EitanTal/hunter/PCB/IMG_20210823_182307683a.jpg

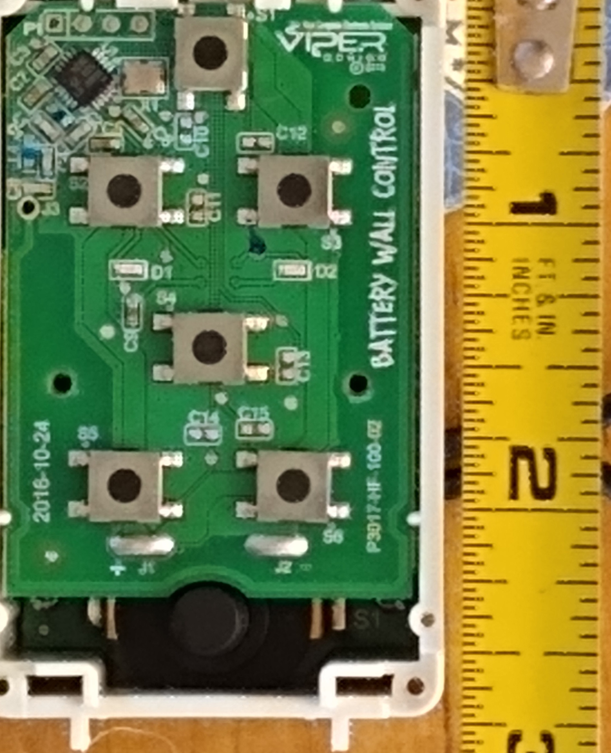
PCB/IMG_20210823_182307683a.jpg
