EitanTal/hunter/circuit/Circuit-ExistingRemote.PNG

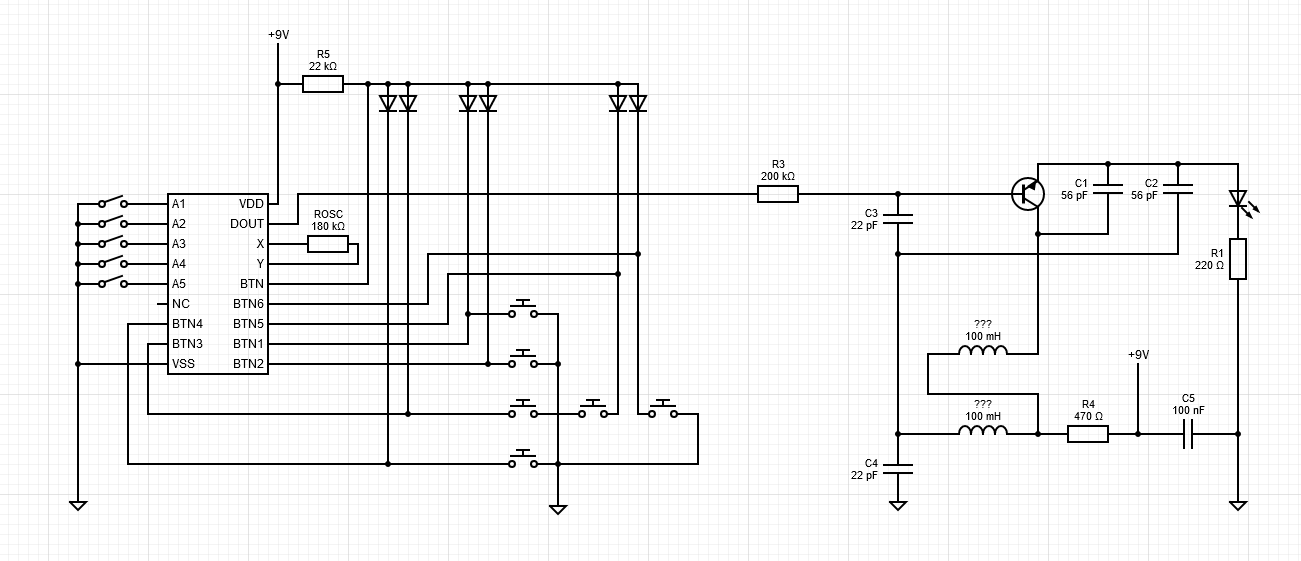
circuit/Circuit-ExistingRemote.PNG
