EitanTal/hunter/PCB/IMG_20210823_162859296.jpg

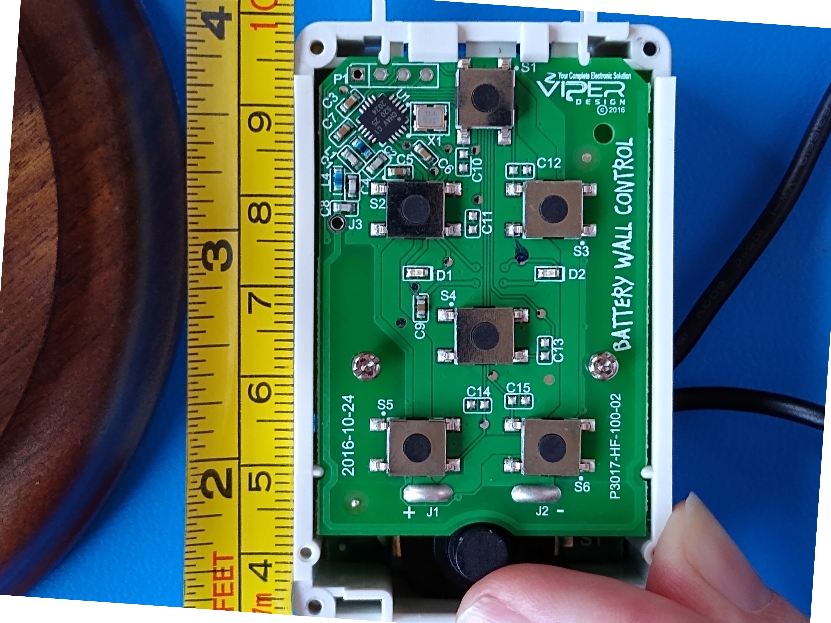
PCB/IMG_20210823_162859296.jpg
