EitanTal/hunter/PCB/other_formfactor.jpg

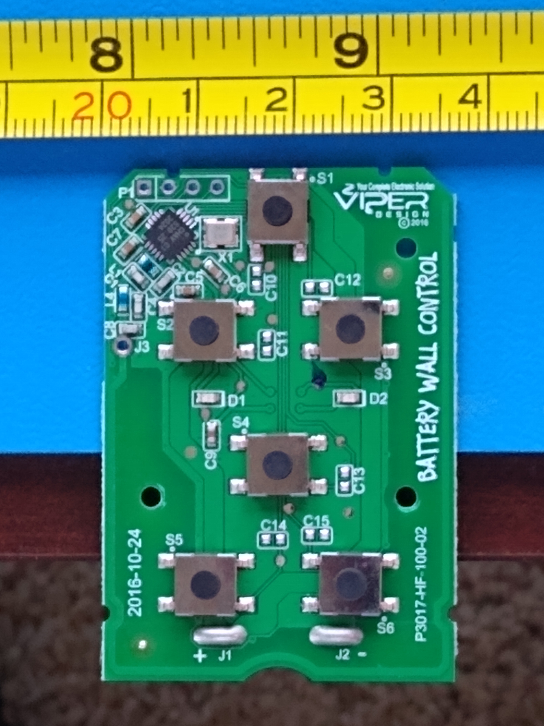
PCB/other_formfactor.jpg
