EitanTal/hunter/SDR/AM-Demodulated.PNG

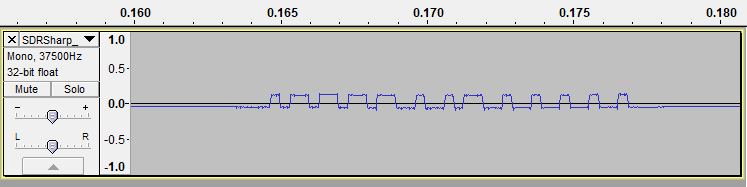
SDR/AM-Demodulated.PNG
