EitanTal/hunter/SDR/SDR_sharp.png

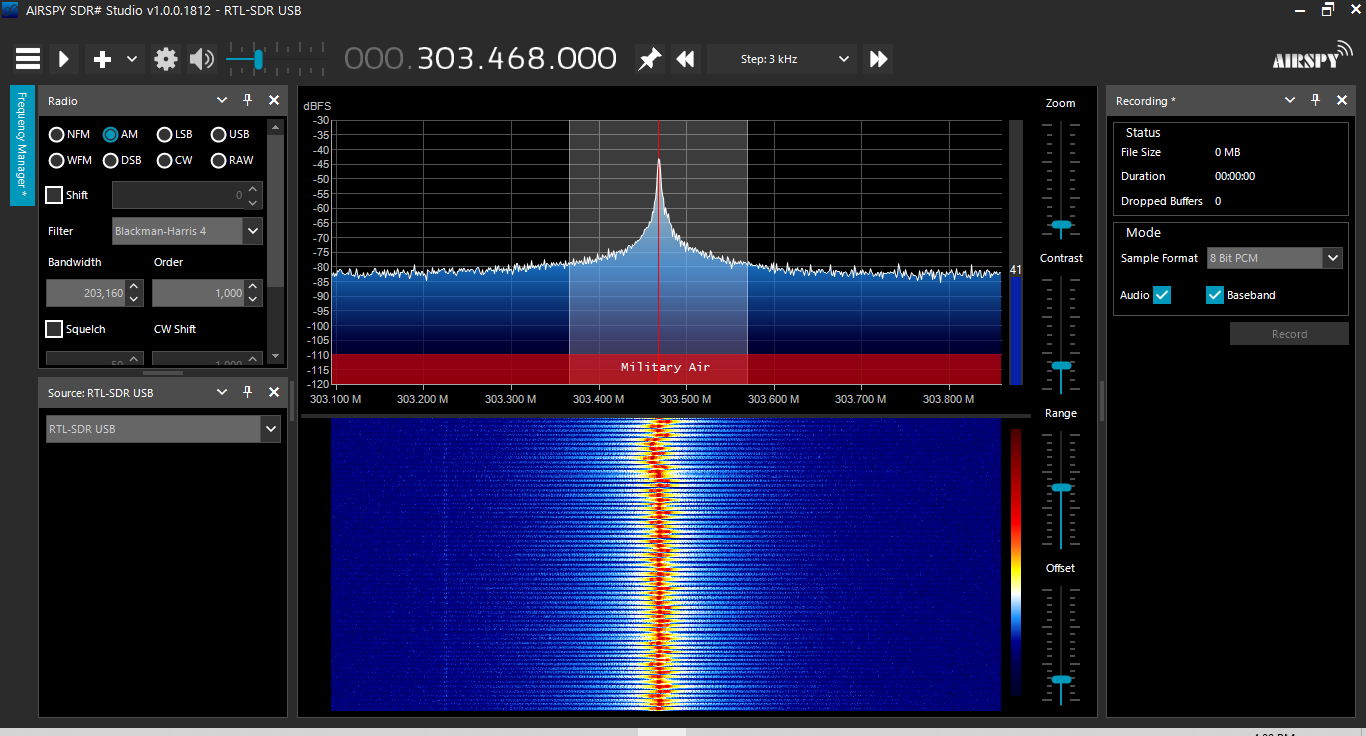
SDR/SDR_sharp.png
