EitanTal/hunter/waveforms/circuit.png

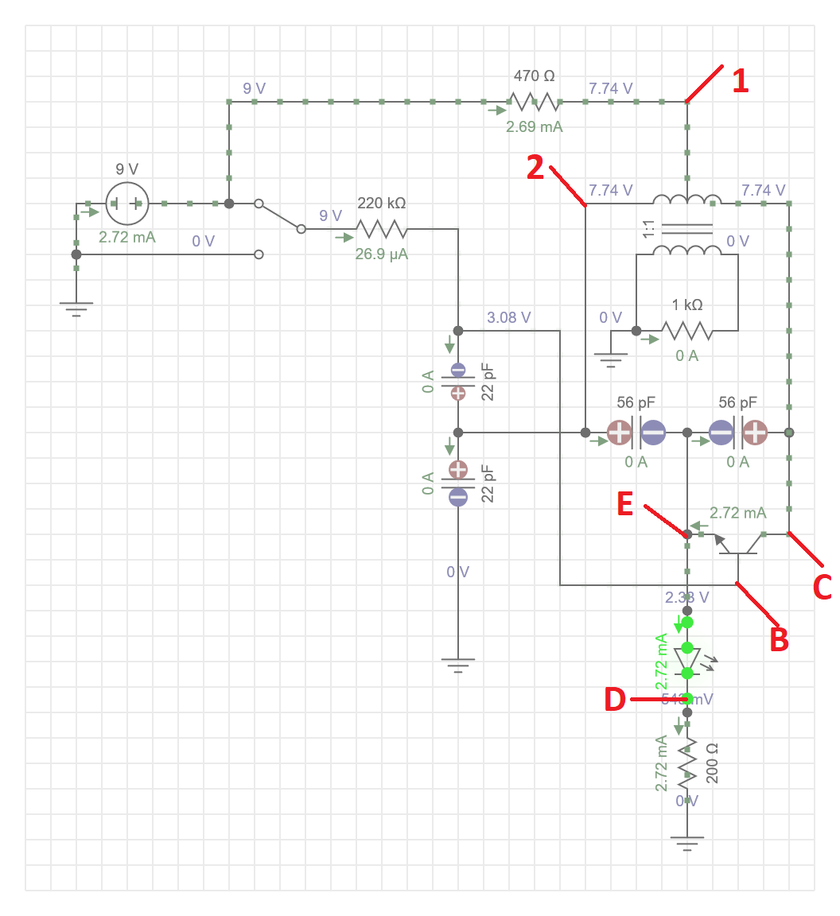
waveforms/circuit.png
