EitanTal/hunter/waveforms/digital_out.png

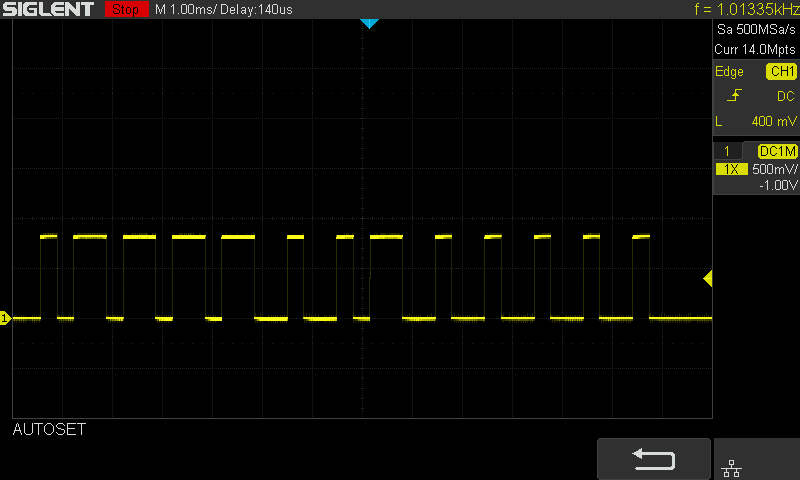
waveforms/digital_out.png
