EitanTal/hunter/waveforms/hunter_base_all.png

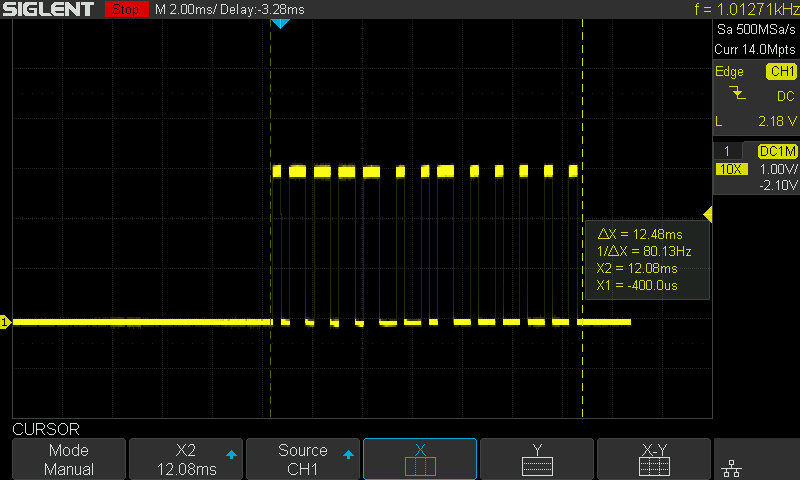
waveforms/hunter_base_all.png
