EitanTal/hunter/waveforms/hunter_base_fall.png

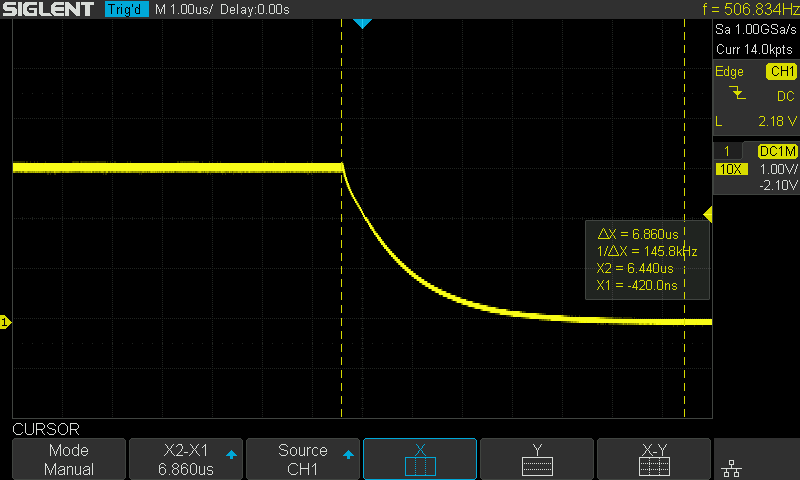
waveforms/hunter_base_fall.png
