EitanTal/hunter/waveforms/hunter_base_h.png

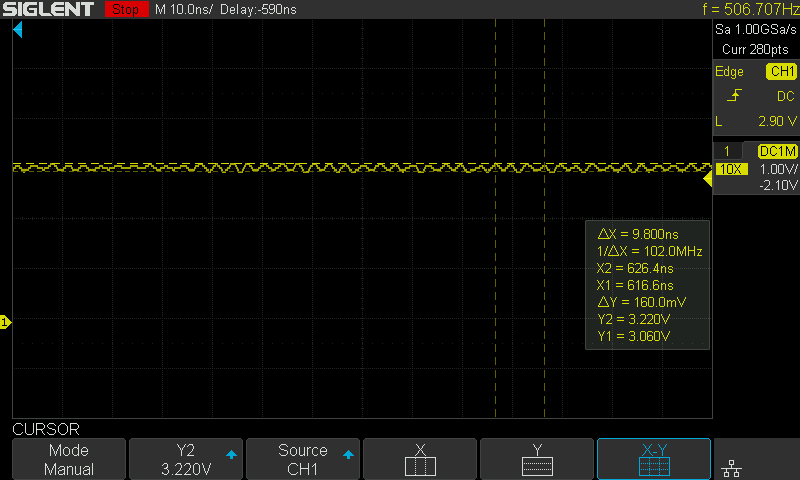
waveforms/hunter_base_h.png
