EitanTal/hunter/waveforms/hunter_base_l.png

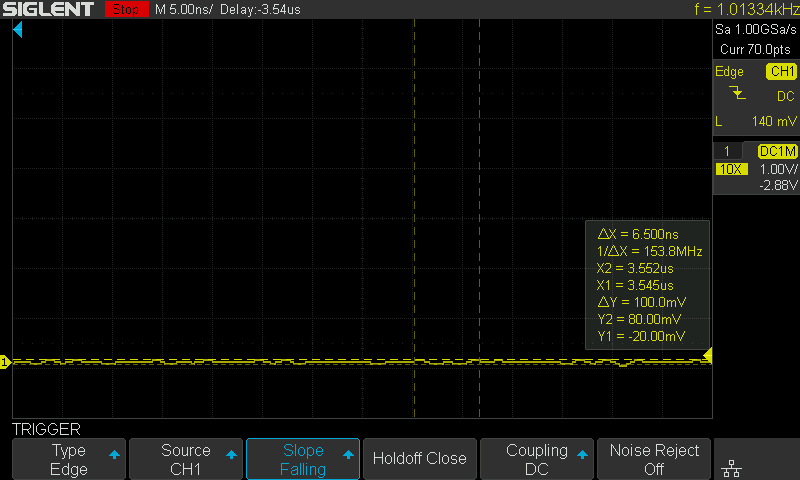
waveforms/hunter_base_l.png
