EitanTal/hunter/waveforms/hunter_collector_all.png

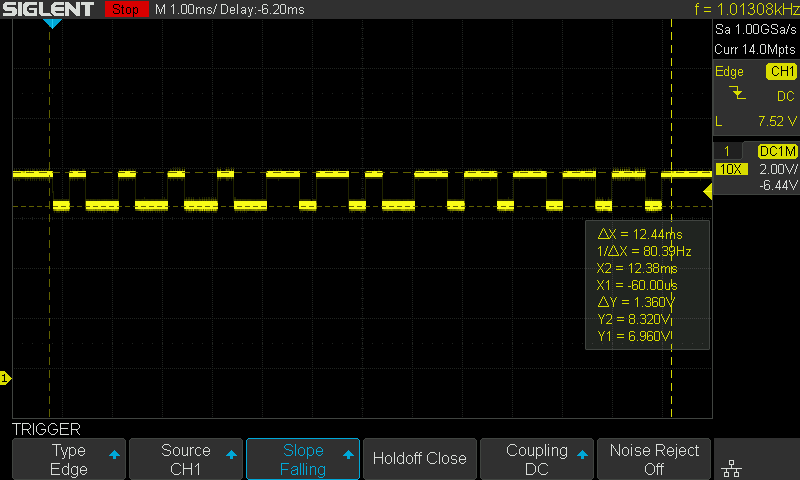
waveforms/hunter_collector_all.png
