EitanTal/hunter/waveforms/hunter_collector_rise.png

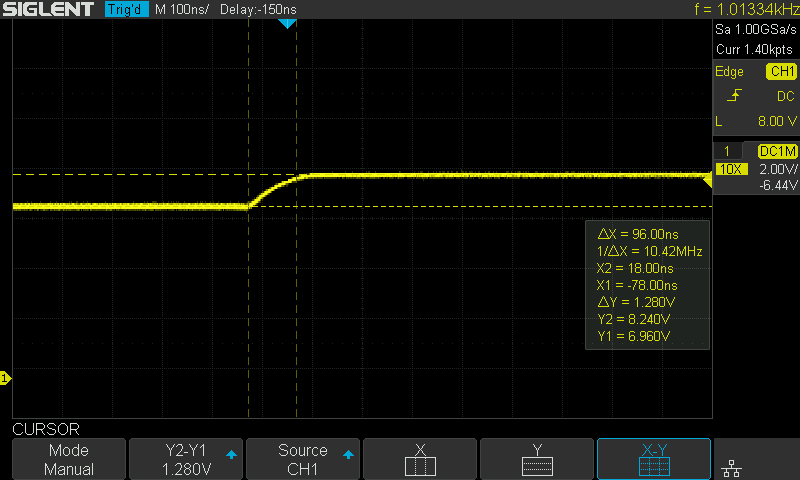
waveforms/hunter_collector_rise.png
