EitanTal/hunter/waveforms/hunter_collector_rise_zoom2.png

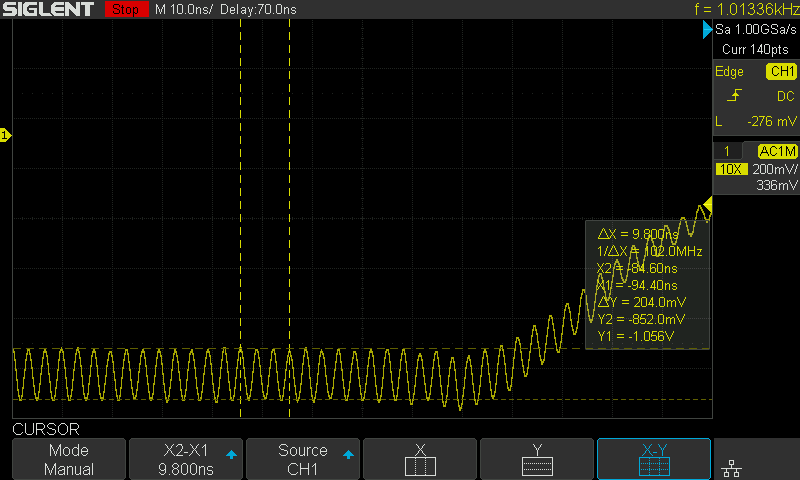
waveforms/hunter_collector_rise_zoom2.png
