EitanTal/hunter/waveforms/hunter_collector_rise_zoom.png

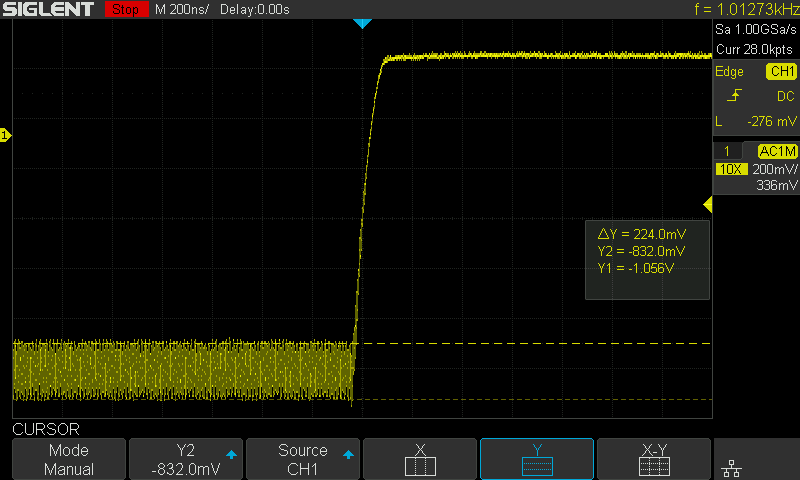
waveforms/hunter_collector_rise_zoom.png
