EitanTal/hunter/waveforms/hunter_diode.png

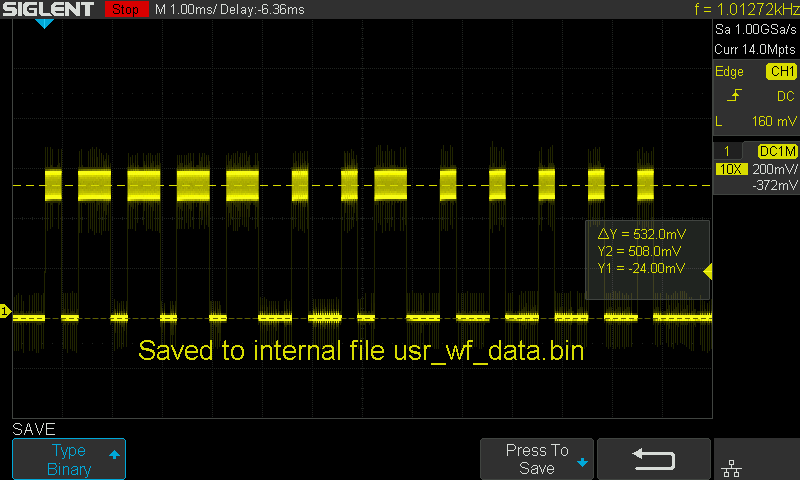
waveforms/hunter_diode.png
