EitanTal/hunter/waveforms/hunter_diode_l.png

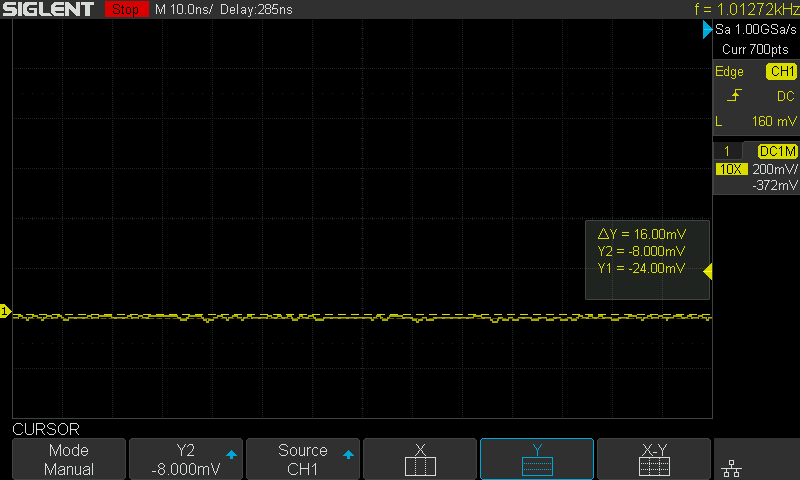
waveforms/hunter_diode_l.png
