EitanTal/hunter/waveforms/hunter_diode_transition.png

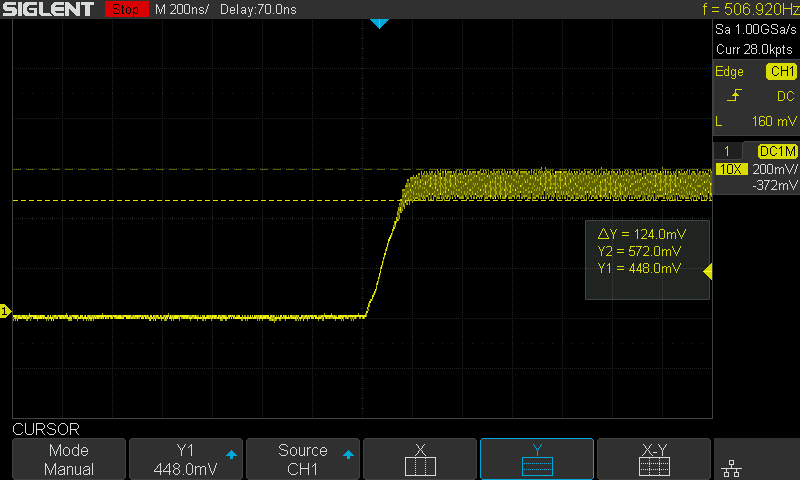
waveforms/hunter_diode_transition.png
