EitanTal/hunter/waveforms/hunter_emitter.png

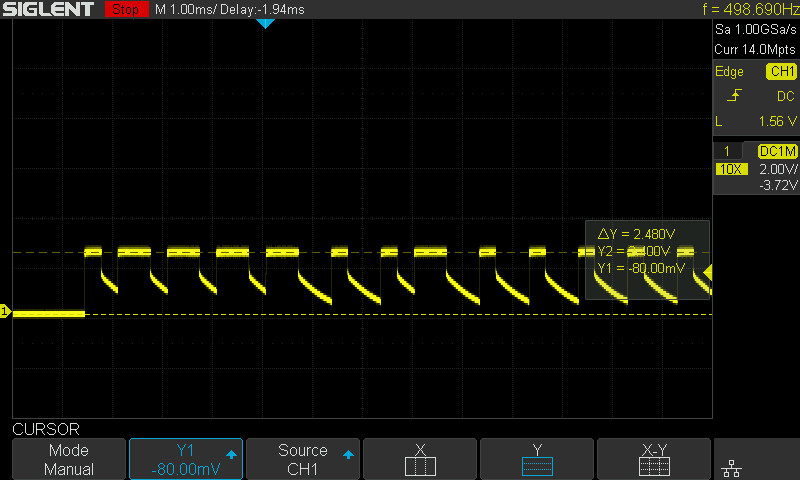
waveforms/hunter_emitter.png
