EitanTal/hunter/waveforms/hunter_emitter_fall.png

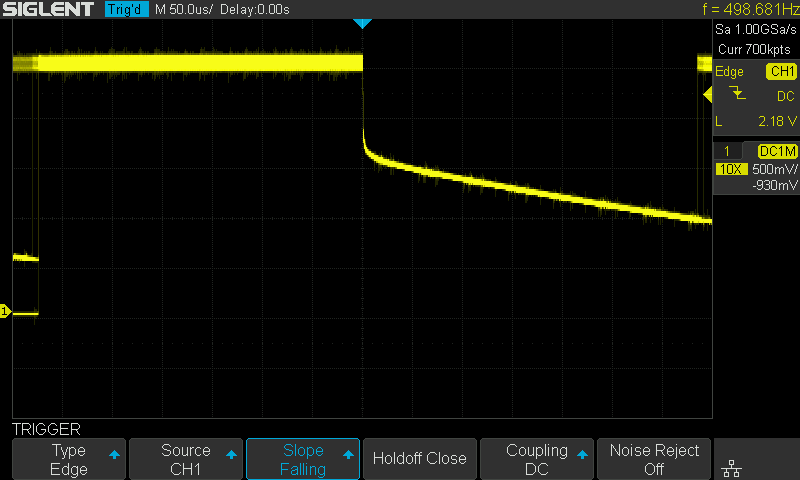
waveforms/hunter_emitter_fall.png
