EitanTal/hunter/waveforms/hunter_emitter_fall_zoom.png

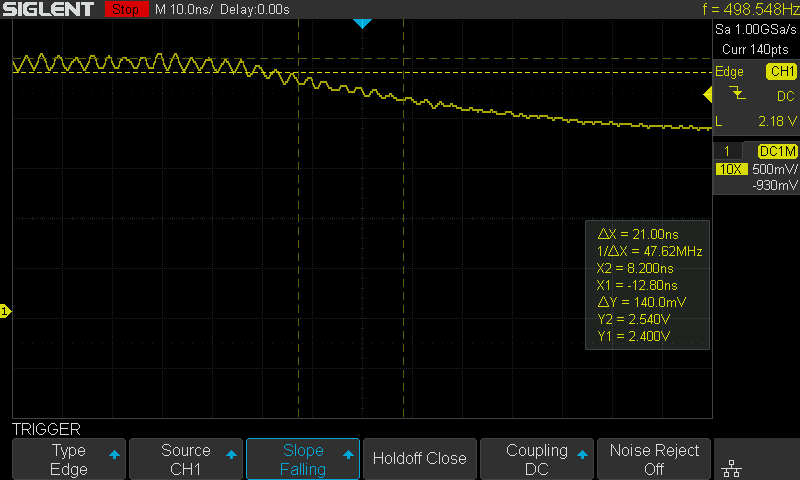
waveforms/hunter_emitter_fall_zoom.png
