EitanTal/hunter/waveforms/hunter_emitter_h.png

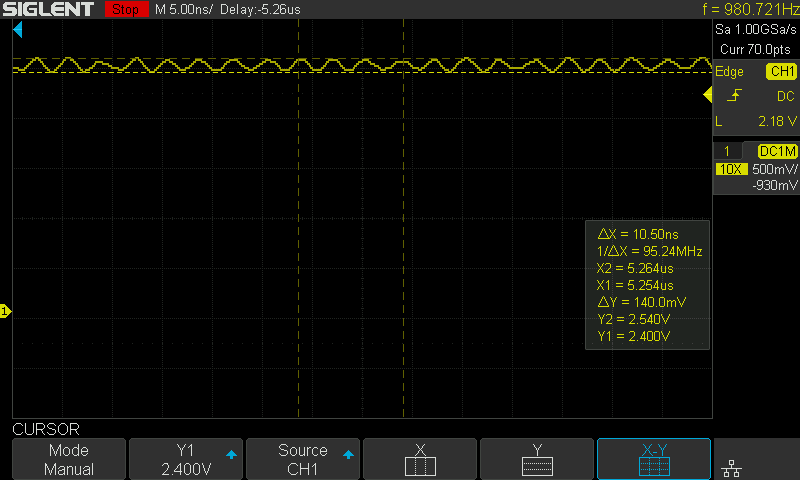
waveforms/hunter_emitter_h.png
