EitanTal/hunter/waveforms/hunter_emitter_l.png

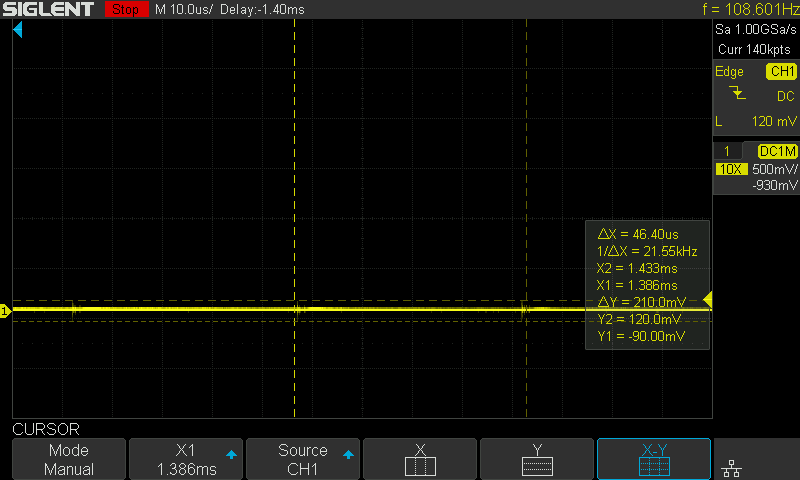
waveforms/hunter_emitter_l.png
