EitanTal/hunter/waveforms/hunter_emitter_rise.png

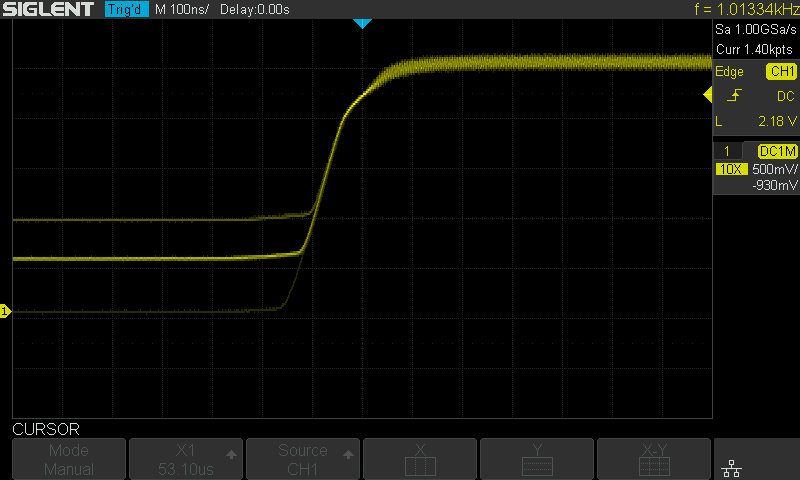
waveforms/hunter_emitter_rise.png
