EitanTal/hunter/waveforms/point1_all.png

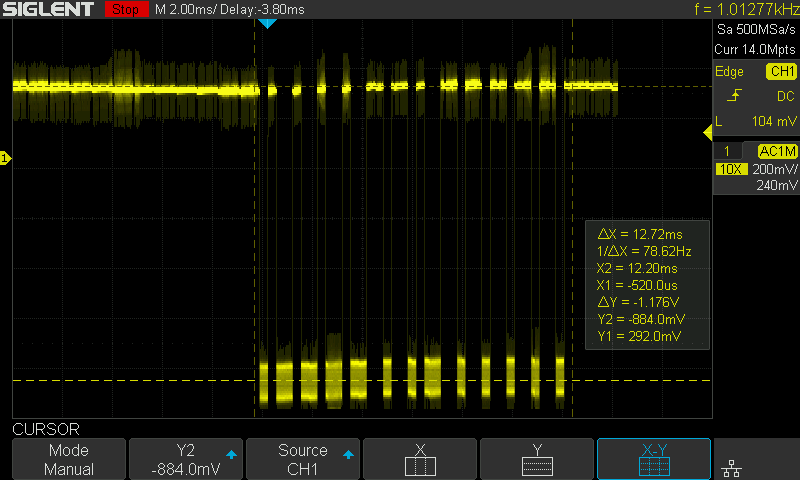
waveforms/point1_all.png
