EitanTal/hunter/waveforms/point1_all_dc.png

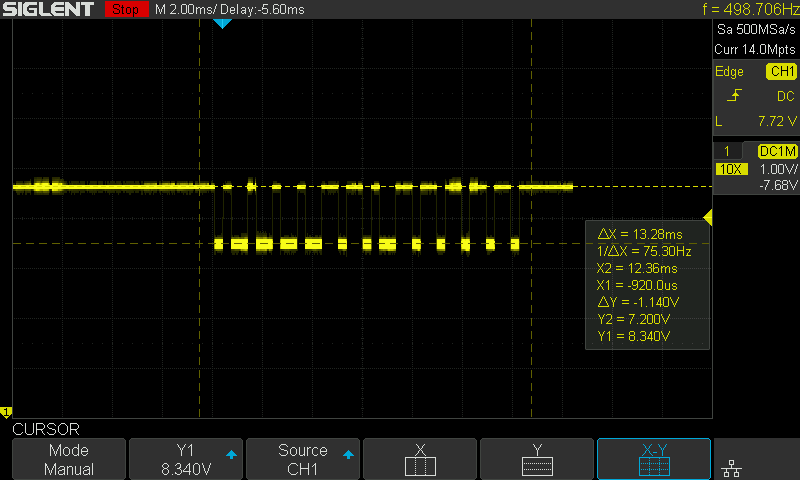
waveforms/point1_all_dc.png
