EitanTal/hunter/waveforms/point1_fall.png

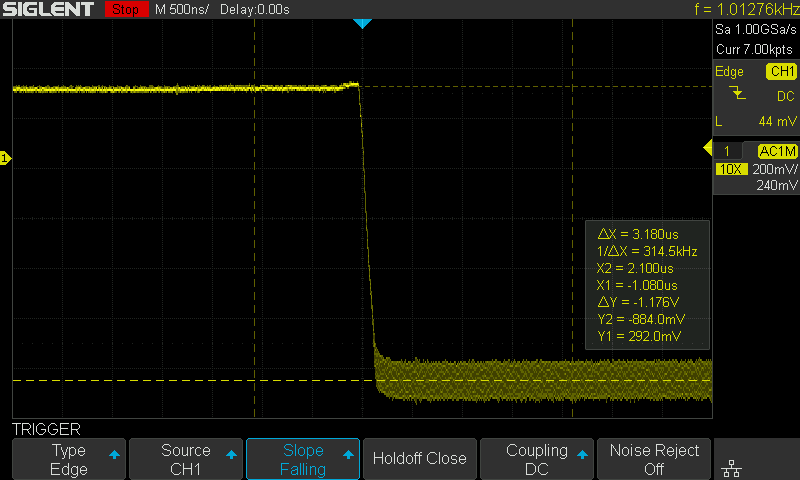
waveforms/point1_fall.png
