EitanTal/hunter/waveforms/point1_fall_dc.png

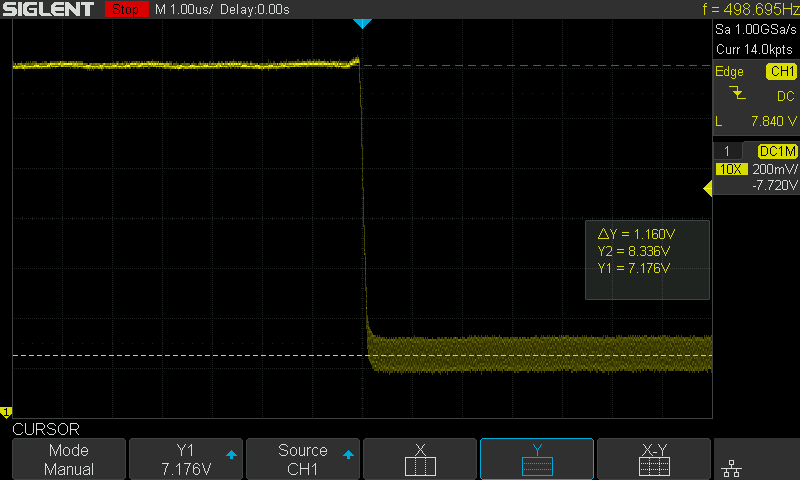
waveforms/point1_fall_dc.png
