EitanTal/hunter/waveforms/point1_fall_zoom.png

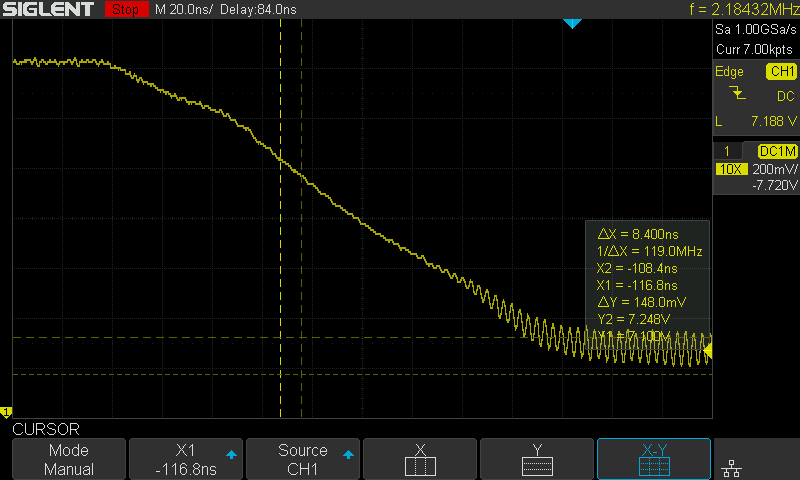
waveforms/point1_fall_zoom.png
