EitanTal/hunter/waveforms/point1_rise.png

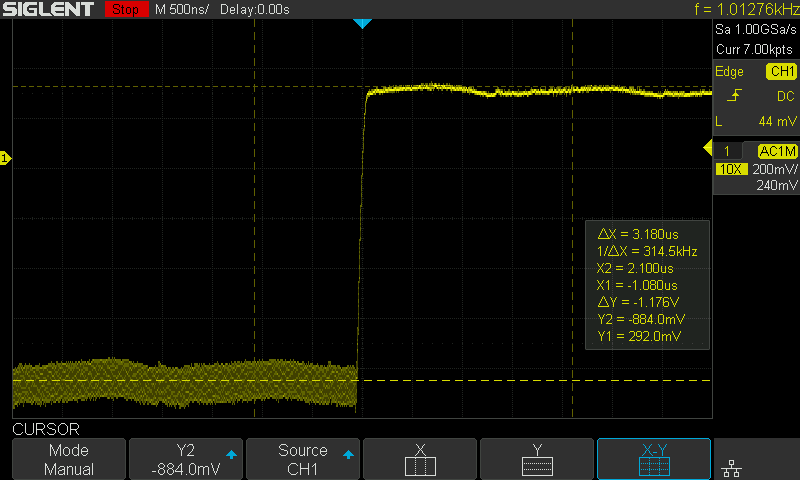
waveforms/point1_rise.png
