EitanTal/hunter/waveforms/point2_all.png

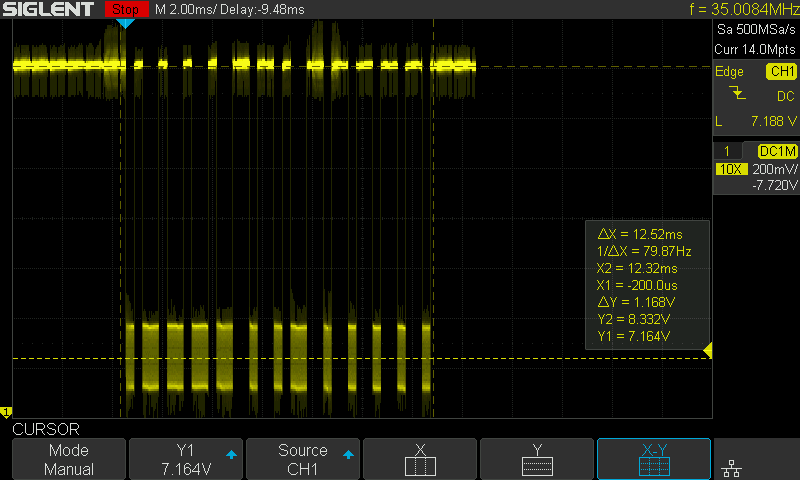
waveforms/point2_all.png
