EitanTal/hunter/waveforms/point2_fall.png

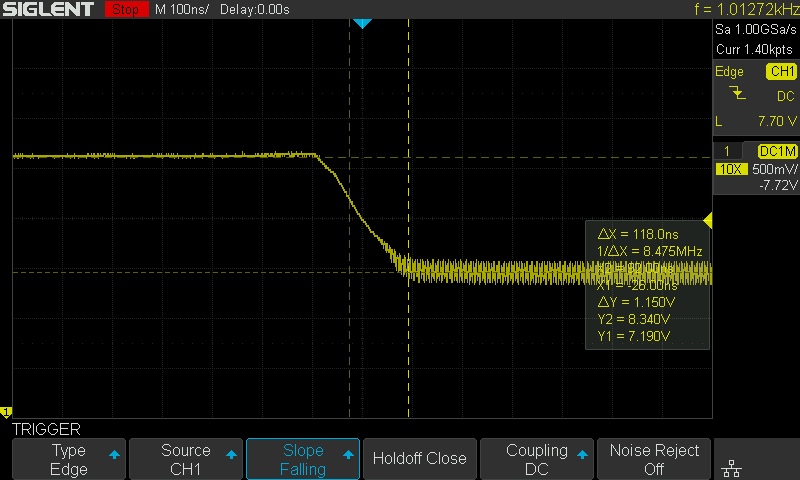
waveforms/point2_fall.png
