EitanTal/hunter/waveforms/point2_fall_zoom.png

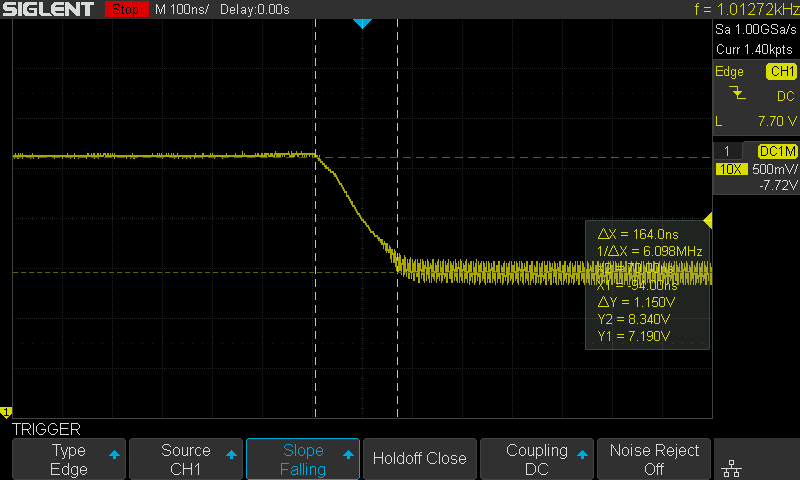
waveforms/point2_fall_zoom.png
