EitanTal/hunter/waveforms/point2_rise.png

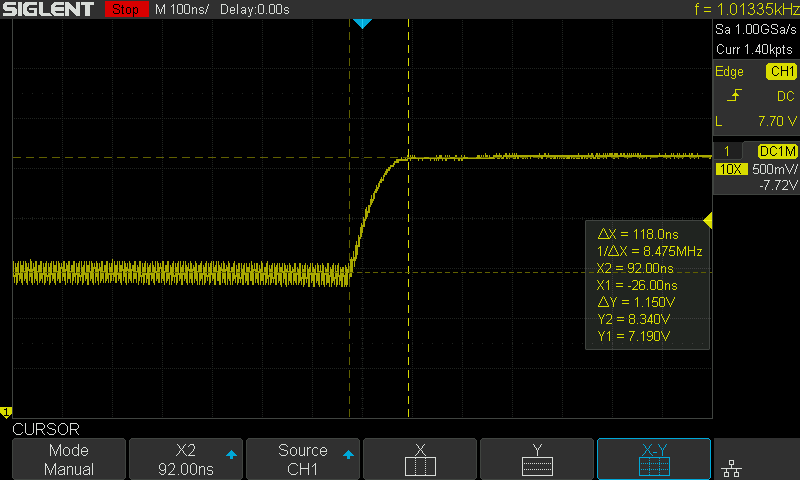
waveforms/point2_rise.png
