EitanTal/hunter/time.c

#include "time.h"
#include "stm8l10x.h"
#include <stdint.h>
#include <stdbool.h>

#define TIM1_AUTO_RELOAD 1000
#define TIM1_PRESCALER 2000

static bool Time_passed;

enum {
    BIT_0 = 1 << 0,
    BIT_1 = 1 << 1,
    BIT_2 = 1 << 2,
    BIT_3 = 1 << 3,
    BIT_4 = 1 << 4,
    BIT_5 = 1 << 5,
    BIT_6 = 1 << 6,
    BIT_7 = 1 << 7
};

enum {
    TIM2_CR1_ENABLE = BIT_0,
    TIM2_CR1_AUTORELOAD = BIT_7,
    TIM2_CCMR_OUTPUT_TOGGLE_MODE = BIT_5 | BIT_4,
    TIM2_CCER1_CC2E = BIT_4,
    TIM2_IER_CC1IE = BIT_1,
    TIM2_IER_UIE = BIT_0,
    TIM2_EGR_UG = BIT_0,
    TIM_PRESCALER_16384 = 0xE,
//    TIM_PRESCALER_8192 = 0xD,
//    TIM_PRESCALER_4096 = 0xC,
    TIM_PRESCALER_2048 = 0xB
//    TIM_PRESCALER_1024 = 0xA
};

#if 0
void TimersSetup(void)
{
    TIM2->ARRH = 0xFF;
    TIM2->ARRL = 0xFF;

    TIM1->ARRH = TIM1_AUTO_RELOAD >> 8;
    TIM1->ARRL = TIM1_AUTO_RELOAD & 0xFF;
    TIM1->PSCRH = TIM1_PRESCALER >> 8;
    TIM1->PSCRL = TIM1_PRESCALER & 0xFF;
    TIM1->EGR = TIM2_EGR_UG; // Reset timer, clear all the things, and apply the prescaler.
    TIM1->CR1 = TIM2_CR1_ENABLE | TIM2_CR1_AUTORELOAD; // Enable the timer
}

bool IsTimePassed(void)
{
    if (Time_passed)
    {
        Time_passed = false;
        return true;
    }
    return false;
}

void ISR_TIM2_UPDATEOVERFLOW(void)
{
    Time_passed = true;
    TIM2->SR1 = 0; // ACK the event
    TIM2->CR1 = 0; // Disable the timer
}

void SetNotification(int seconds_in_future)
{
    uint16_t ticks = (seconds_in_future * 122); // (roughly)
    if (ticks <= 0) ticks = 1;
    TIM2->CR1 = 0; // Disable the timer
    TIM2->PSCR = TIM_PRESCALER_16384;
    TIM2->CCR1H = ticks >> 8;
    TIM2->CCR1L = ticks & 0xFF;
    TIM2->CNTRH = 0;
    TIM2->CNTRL = 0;
    TIM2->IER = TIM2_IER_CC1IE; // Enable the timer interrupt
    TIM2->EGR = TIM2_EGR_UG; // Reset timer, clear all the things, and apply the prescaler.
    Time_passed = false; // Disable a would-be pending event
    TIM2->CR1 = TIM2_CR1_ENABLE; // Enable the timer
}

int get_milliseconds_now(void)
{
    // ! must be read in this order!
    uint8_t a = TIM1->CNTRH;
    uint8_t b = TIM1->CNTRL;
    
    uint16_t val = (a << 8) | b;
}

int get_milliseconds_since(int when)
{
    int now = get_milliseconds_now();

    int diff = now - when;
    if (diff < 0) diff += TIM1_AUTO_RELOAD;
    return diff;
}
#endif

void delayMicroseconds(int time)
{
    // ! Arduino
    int i = 0;
    for (i = 0; i < time; i++)
    {
        __asm("NOP");
    }
}

void delay(int time)
{
    // ! Arduino
    int i;
    for (i = 0; i < time; i++ )
    {
        delayMicroseconds(75);
    }
}
